mseri/pplofthesoil/probe/case/1.png

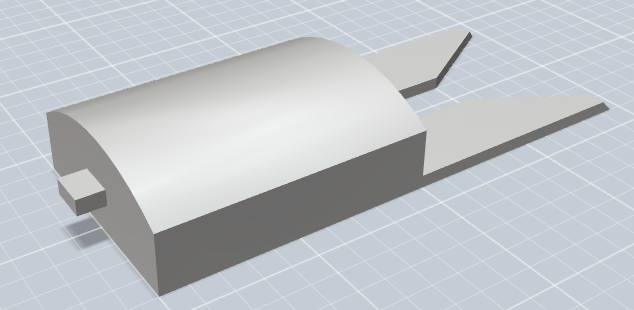
probe/case/1.png
