mseri/pplofthesoil/probe/case/2.png

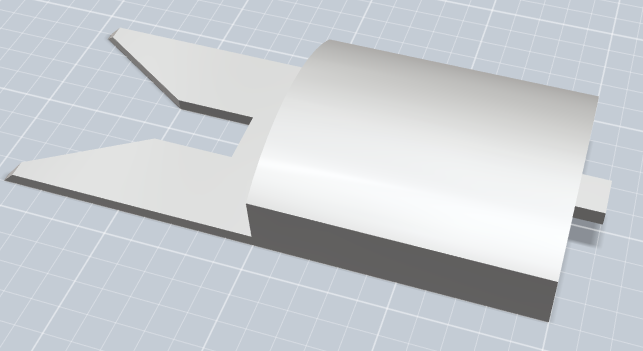
probe/case/2.png
