mseri/pplofthesoil/probe/case/3.png

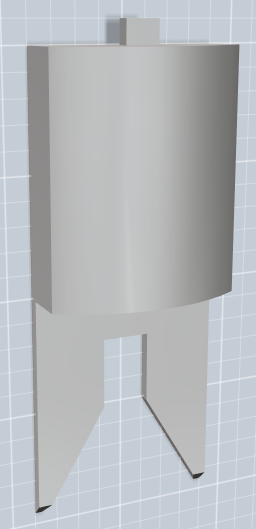
probe/case/3.png
