mseri/pplofthesoil/probe/eagle/brd.png

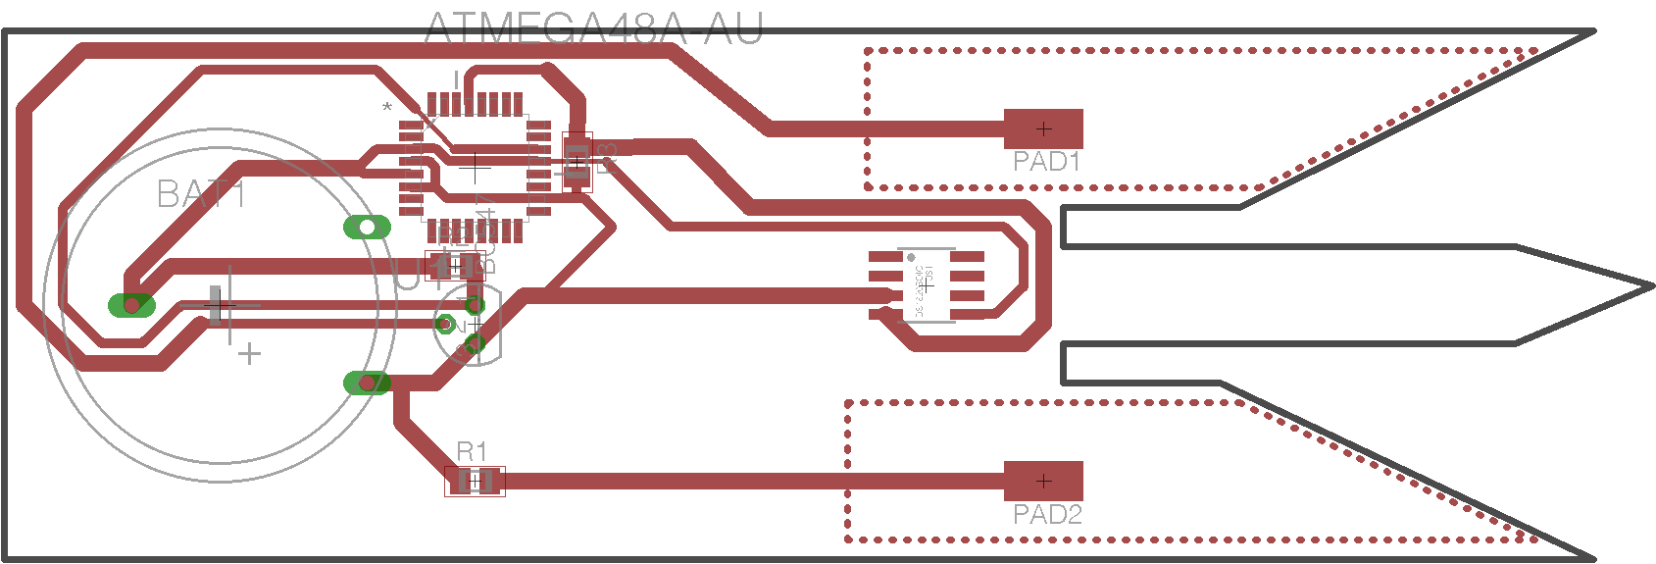
probe/eagle/brd.png
