mseri/pplofthesoil/probe/eagle/eagleUp/eagleUp_cheapboard1.1_board_bottom.jpg

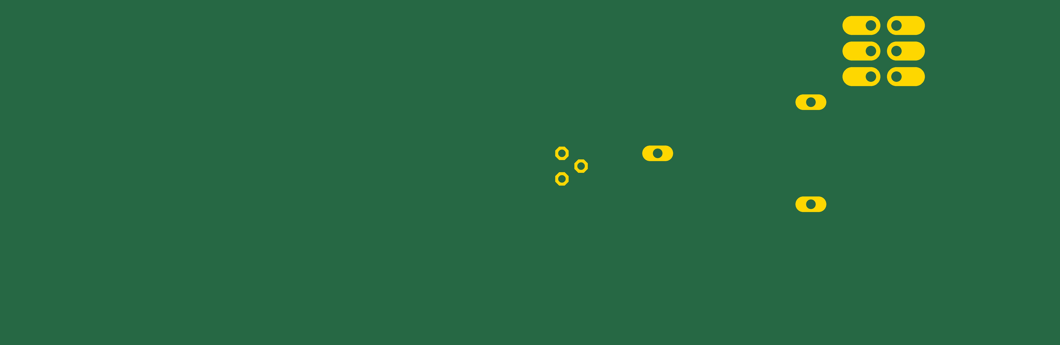
probe/eagle/eagleUp/eagleUp_cheapboard1.1_board_bottom.jpg
