mseri/pplofthesoil/probe/eagle/eagleUp/eagleUp_cheapboard1.1_bottom.png

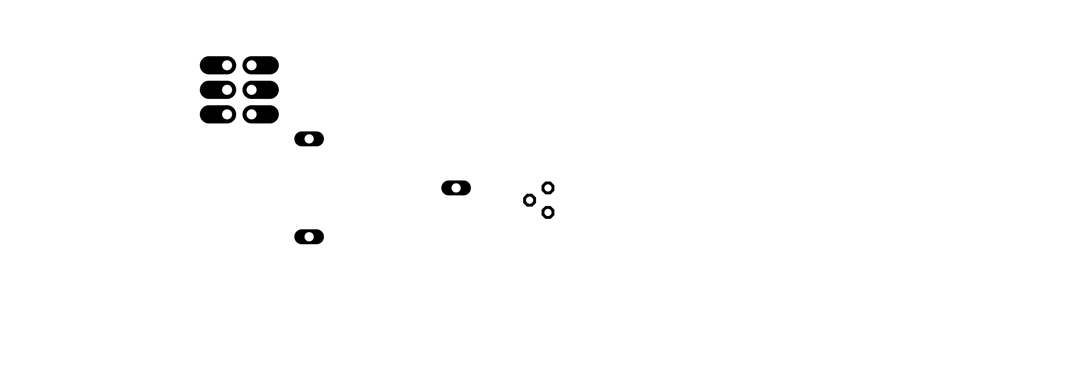
probe/eagle/eagleUp/eagleUp_cheapboard1.1_bottom.png
