mseri/pplofthesoil/probe/eagle/eagleUp/eagleUp_cheapboard1.1_imagesize.png

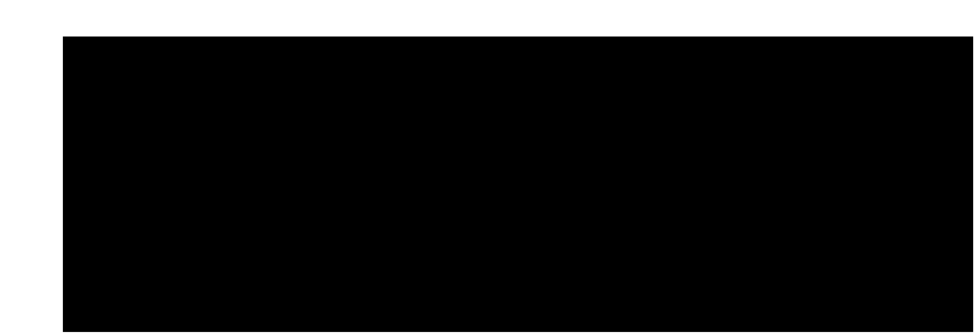
probe/eagle/eagleUp/eagleUp_cheapboard1.1_imagesize.png
