mseri/pplofthesoil/probe/eagle/eagleUp/eagleUp_cheapboard1.1_outline.png

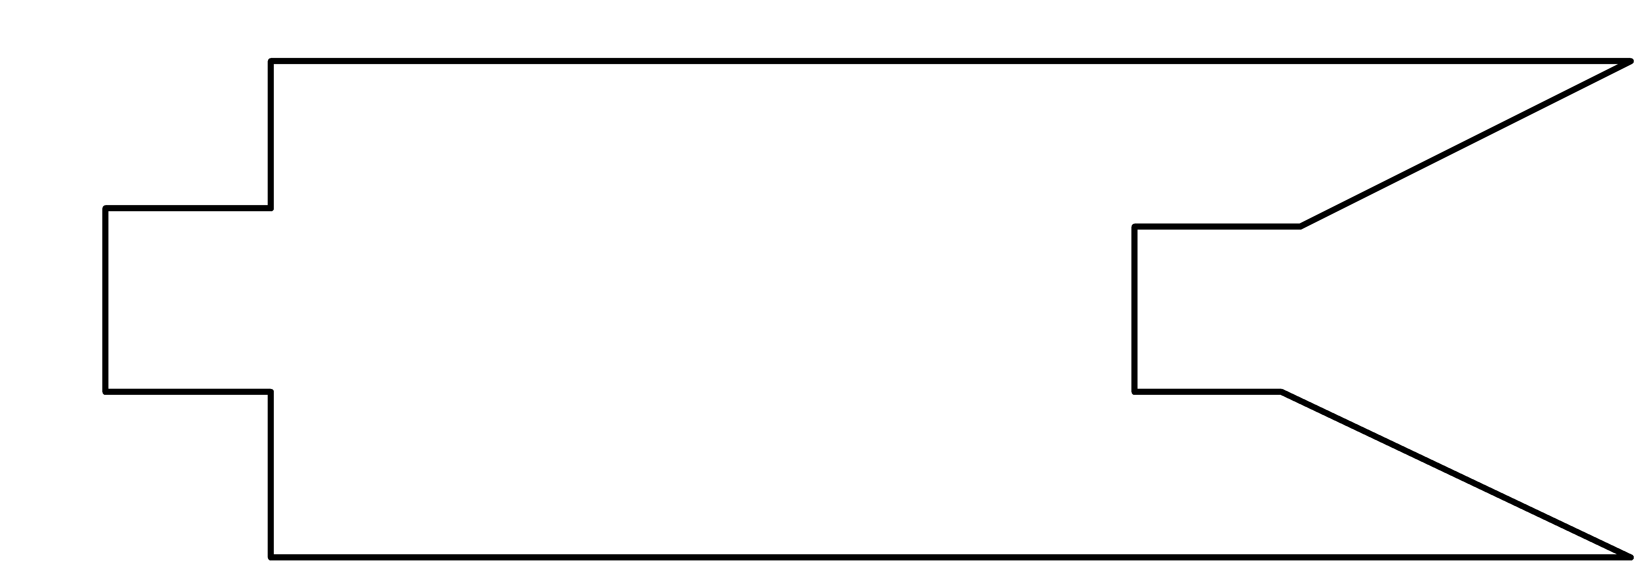
probe/eagle/eagleUp/eagleUp_cheapboard1.1_outline.png
