mseri/pplofthesoil/probe/eagle/eagleUp/eagleUp_cheapboard1.1_top.png

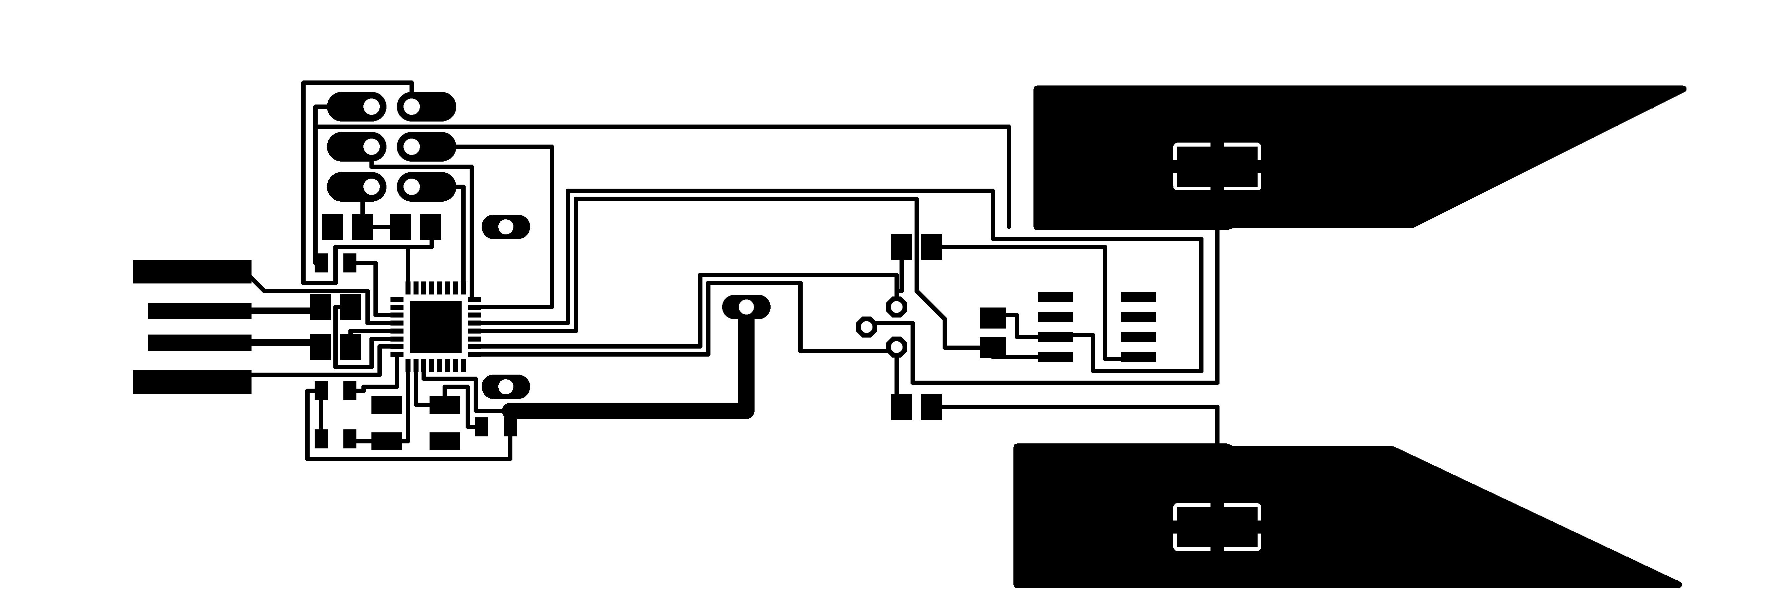
probe/eagle/eagleUp/eagleUp_cheapboard1.1_top.png
