mseri/pplofthesoil/probe/eagle/eagleUp/eagleUp_cheapboard1.1_top_mask.png

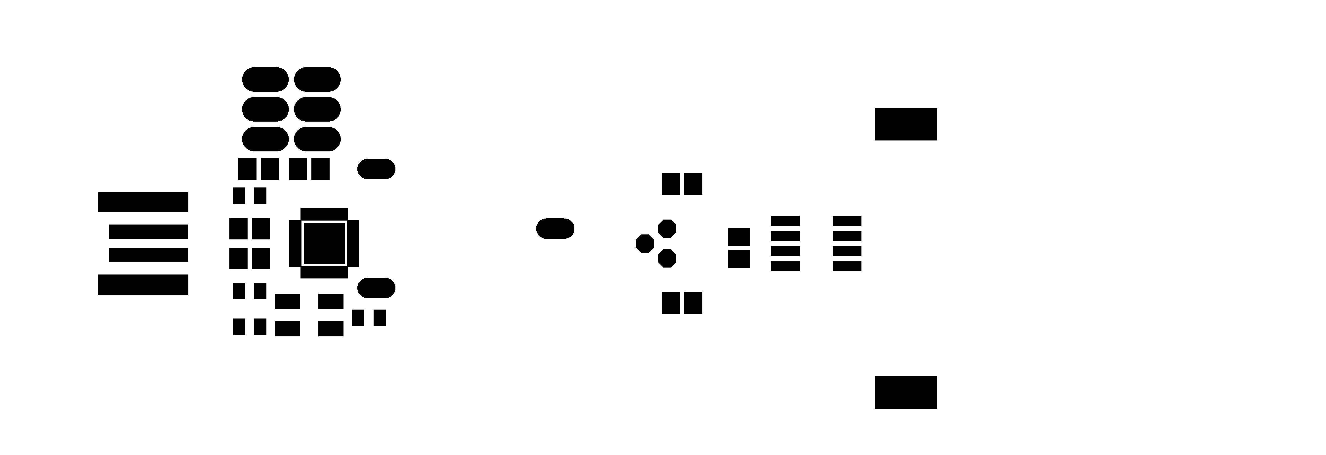
probe/eagle/eagleUp/eagleUp_cheapboard1.1_top_mask.png
