mseri/pplofthesoil/probe/eagle/eagleUp/eagleUp_cheapboard1.1_top_silk.png

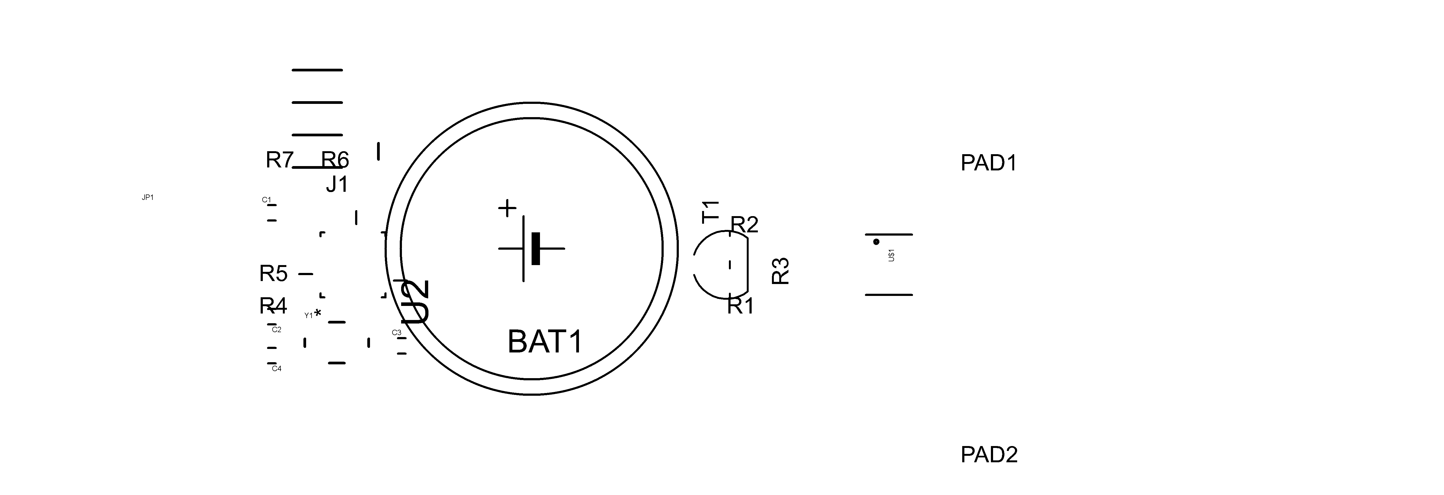
probe/eagle/eagleUp/eagleUp_cheapboard1.1_top_silk.png
