mseri/pplofthesoil/probe/eagle/eagleUp/Full Model 2013-04-24 00565900000.jpg

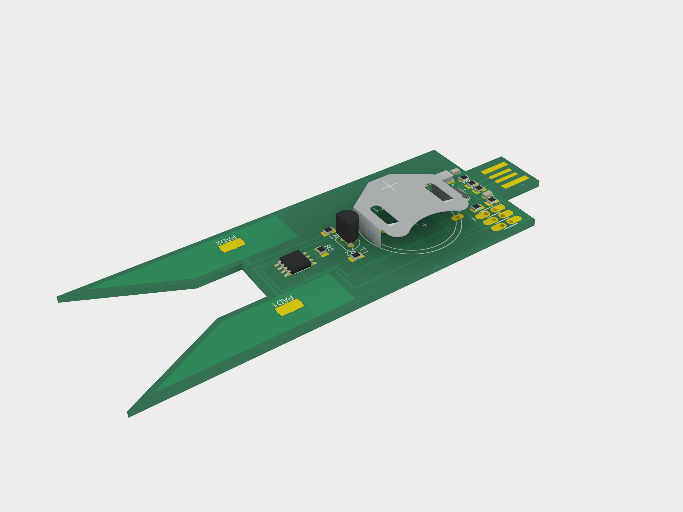
probe/eagle/eagleUp/Full Model 2013-04-24 00565900000.jpg
