mseri/pplofthesoil/probe/eagle/eagleUp/Full Model 2013-04-24 01223300000.jpg

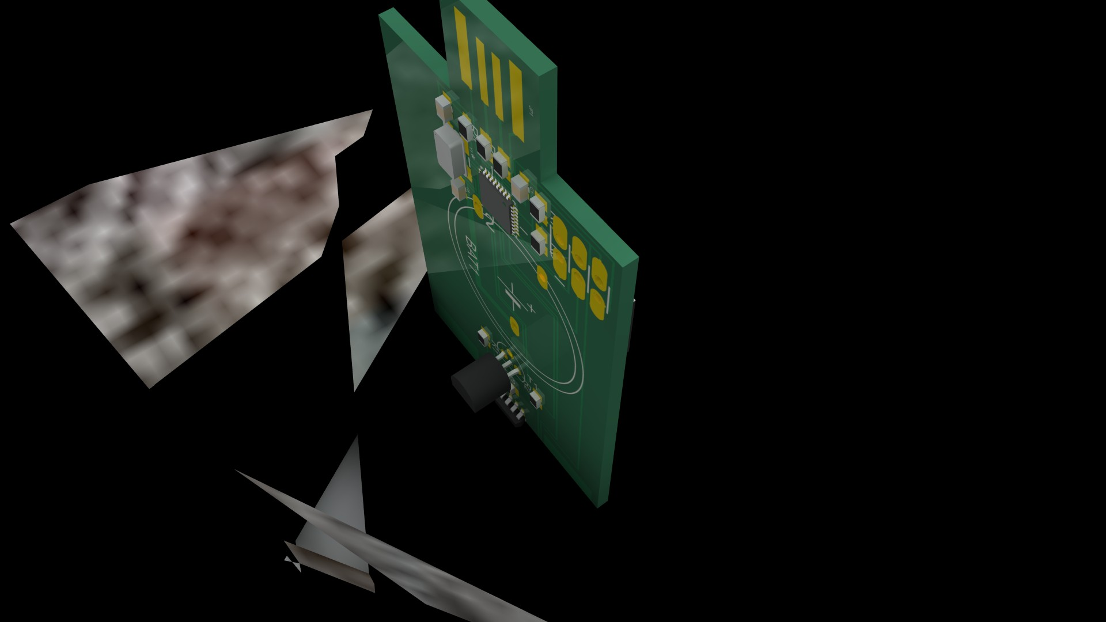
probe/eagle/eagleUp/Full Model 2013-04-24 01223300000.jpg
