mseri/pplofthesoil/probe/eagle/eagleUp/Full Model 2013-04-24 01285800000.jpg

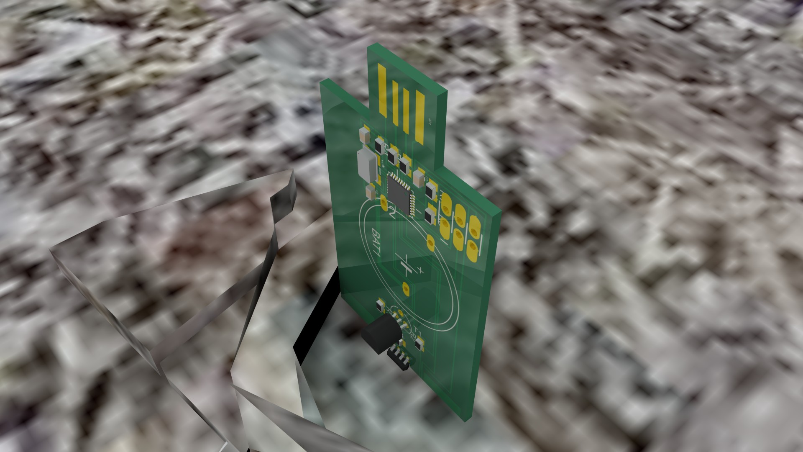
probe/eagle/eagleUp/Full Model 2013-04-24 01285800000.jpg
