mseri/pplofthesoil/probe/eagle/eagleUp/Full Model Rubberised 2013-04-24 14181000000.jpg

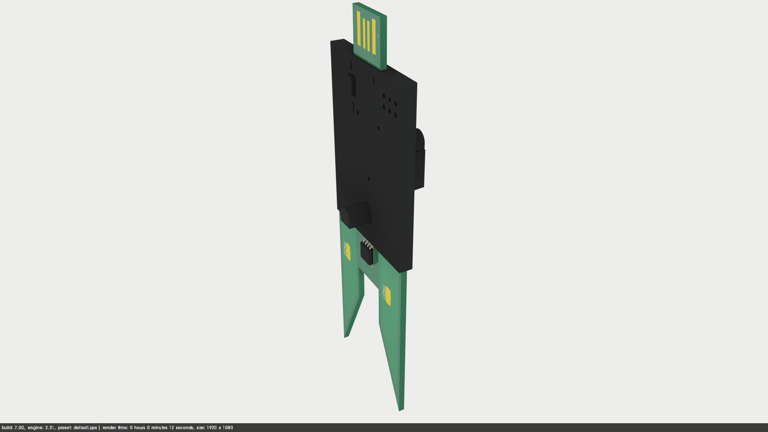
probe/eagle/eagleUp/Full Model Rubberised 2013-04-24 14181000000.jpg
