mseri/pplofthesoil/probe/eagle/eagleUp/Full Model Rubberised 2013-04-24 14191500000.jpg

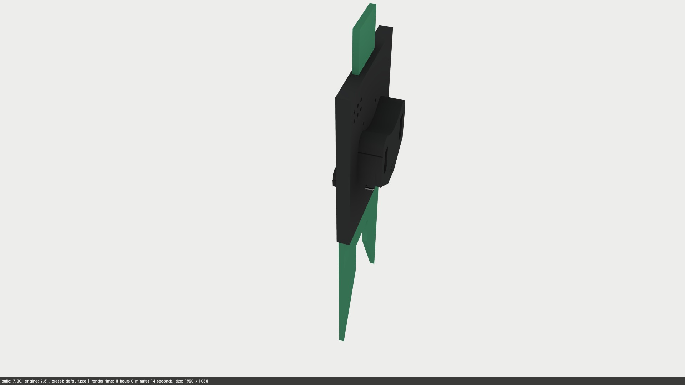
probe/eagle/eagleUp/Full Model Rubberised 2013-04-24 14191500000.jpg
