mseri/pplofthesoil/probe/eagle/sch.png

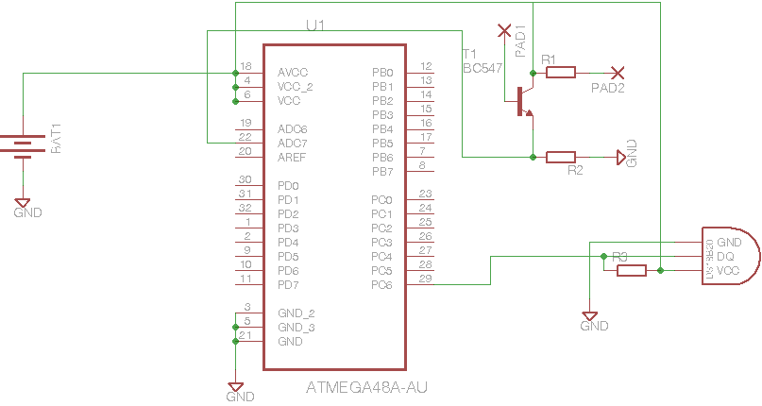
probe/eagle/sch.png
